yellobyte/USB-Atmel-In-Circuit-Programmer/PCB/Board.JPG

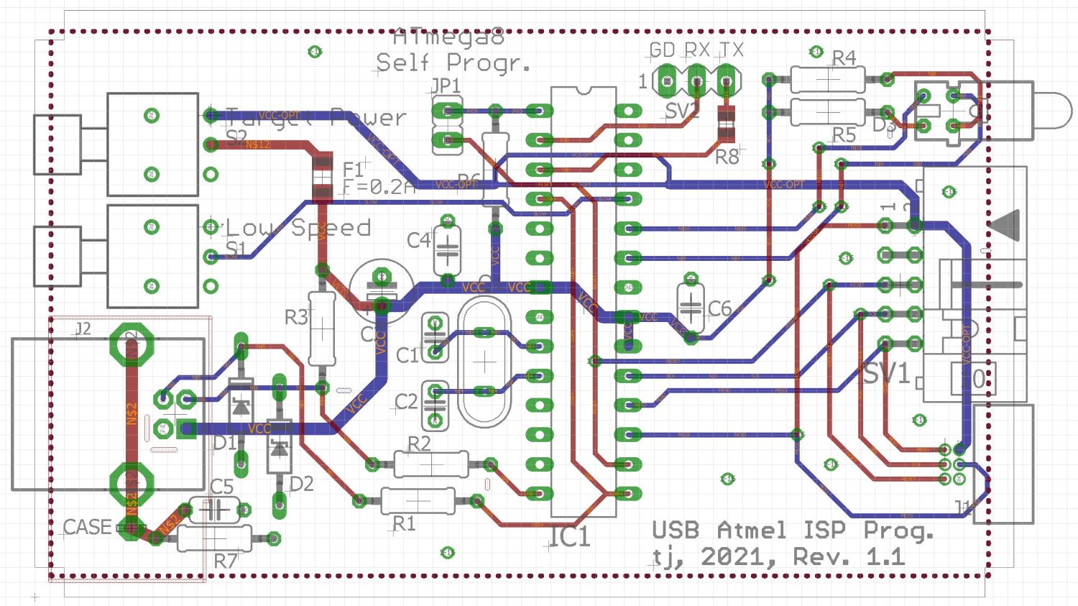
PCB/Board.JPG
