yellobyte/USB-Atmel-In-Circuit-Programmer/PCB/BoardBottom.JPG

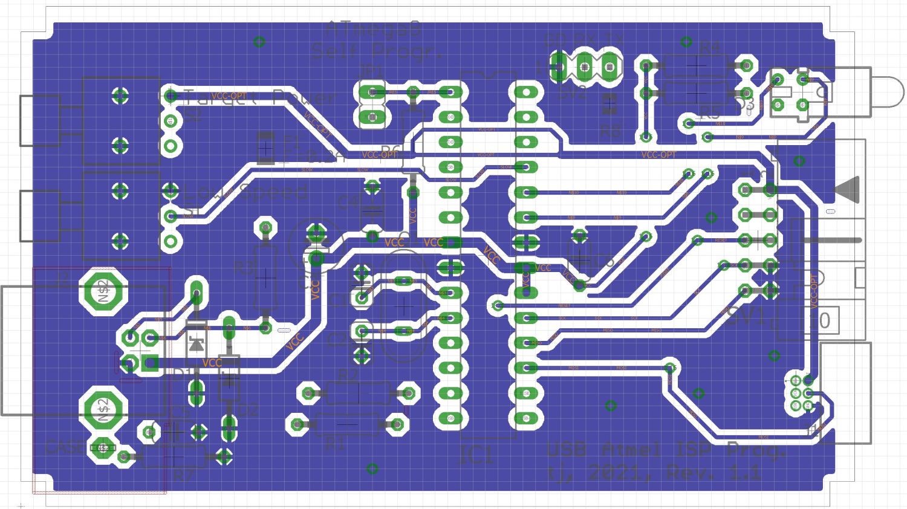
PCB/BoardBottom.JPG
