yellobyte/USB-Atmel-In-Circuit-Programmer/PCB/BoardTop.JPG

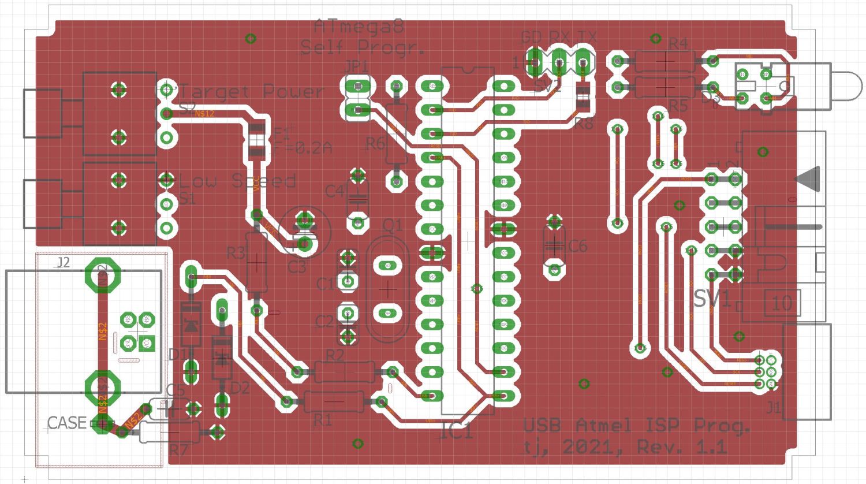
PCB/BoardTop.JPG
